Protocentral/Kalam/Firmware/Screenshot/baudrate.jpg

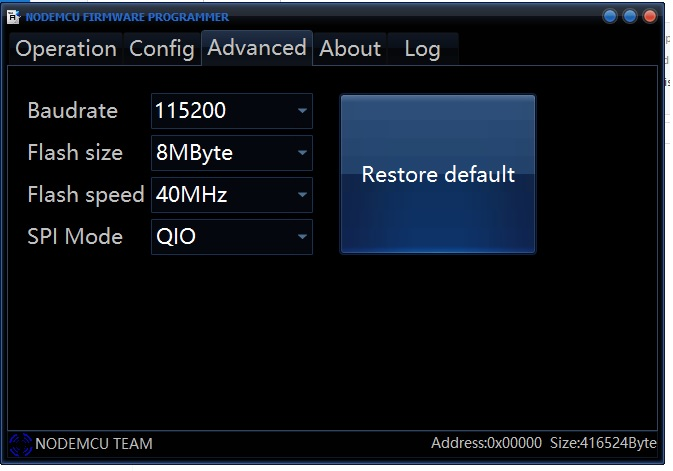
Firmware/Screenshot/baudrate.jpg
