Protocentral/Kalam/Firmware/Screenshot/flashing.jpg

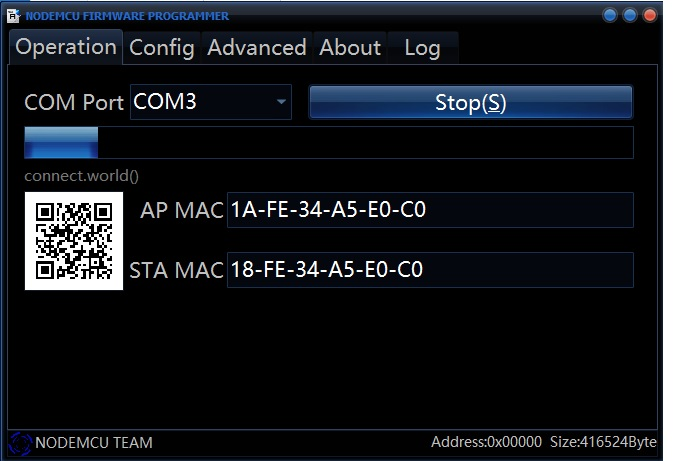
Firmware/Screenshot/flashing.jpg
