Protocentral/Kalam/Firmware/Screenshot/ComPort_Selection.jpg

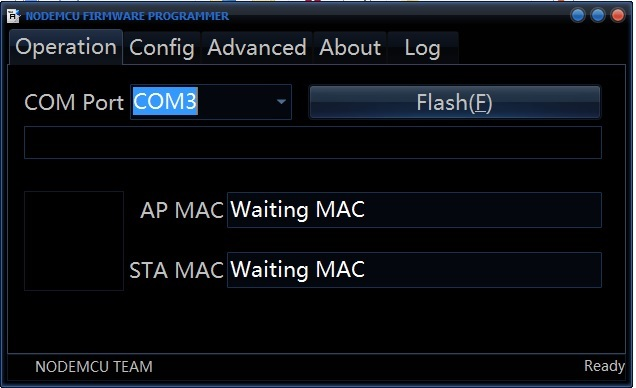
Firmware/Screenshot/ComPort_Selection.jpg
