Protocentral/Kalam/Firmware/Screenshot/Config.jpg

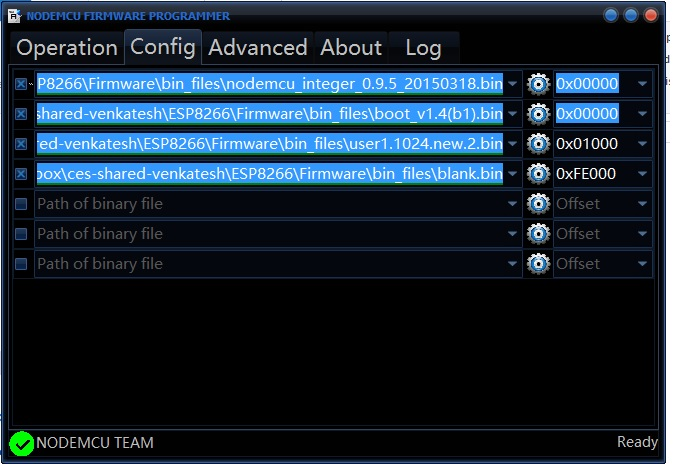
Firmware/Screenshot/Config.jpg
